frankyhub/Wetterstation/png/barometer3.jpg

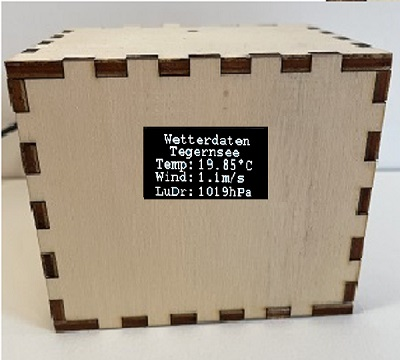
png/barometer3.jpg
