frankyhub/Wetterstation/png/DHT11_Verdrahtung.png

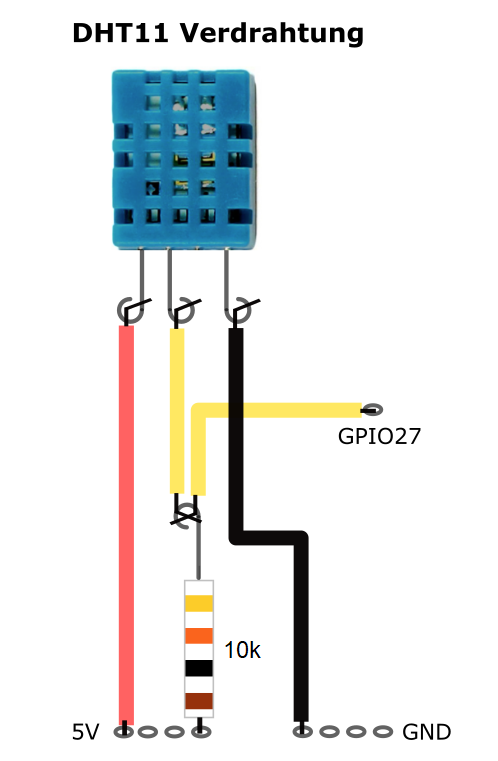
png/DHT11_Verdrahtung.png
